jabr0ni/epaper-hat/Software/epaper-image-converter-QT/ePaperProperties.h

#ifndef EPAPERPROPERTIES_H
#define EPAPERPROPERTIES_H

/**
 *  Properties for 2.13 inch E-Paper display
+--------------------------+----------------------+-------------------+-----------------------------+
| Parameter               | Specification         | Unit              | Remark                      |
+--------------------------+----------------------+-------------------+-----------------------------+
| Screen Size             | 2.13                  | Inch              |                             |
| Display Resolution      | 122(H) × 250(V)       | Pixel             | Dpi: 130                    |
| Active Area             | 23.7046 × 48.55       | mm                |                             |
| Pixel Pitch             | 0.1943 × 0.1942       | mm                |                             |
| Pixel Configuration     | Square                |                   |                             |
| Outline Dimension       | 29.2(H) × 59.2(V) × 1.0(D) | mm          |                             |
| Weight                  | (not specified)        | g                 |                             |
+--------------------------+----------------------+-------------------+-----------------------------+
*/

#define EPAPER_DISPLAY_PX_H     122
#define EPAPER_DISPLAY_PX_W     250

#endif // EPAPERPROPERTIES_H
